NNNILabs/Pulsed-Laser-Driver/Software/Simulation/LT1193 Diff Follower GaN Simple.asc

C1: cap; 33p
C2: cap; 10p
D1: schottky; BAT54
L1: ind; 10n
R2: res; 100
R3: res; 250
SHUNT: res; 0.5
U1: LT1193
U2: GaN_LTspice_GS66502B_L3V4P1
V1: voltage; 8
V2: voltage; 8
V3: voltage; PULSE(0 2.5 100n 1p 1p 100n)
V4: voltage; 500; Rser=1
Named nets: 0, -5, +5, input, output, gate
.tran 300n
