NNNILabs/Pulsed-Laser-Driver/Software/Simulation/Simple Follower nonGaN.asc

C1: cap; 10p
L1: ind; 10n; Rser=0.1
M1: NMOS; AON6992_Bottom
R1: res; 50
SHUNT: res; 0.5
V1: voltage; PULSE(0 4.545 1u 500p 500p 1u); Rser=1
V2: voltage; 30; Rser=0.1
Named nets: 0, gate, source, drain, in
.tran 3u
