NNNILabs/Pulsed-Laser-Driver/Software/Simulation/Simple Follower.asc

C1: cap; 10p
L1: ind; 10n; Rser=0.1
R1: res; 220
R2: res; 0.01
SHUNT: res; 0.5
U1: GaN_LTspice_GS-065-008-1-L_L3V4P1
V1: voltage; PULSE(0 4.625 100n 500p 500p 100n); Rser=1
V2: voltage; 500; Rser=0.1
Named nets: 0, gate, source, drain, in
.tran 300n
