NNNILabs/Pulsed-Laser-Driver/Software/Simulation/LT1193 Diff Follower.asc

C1: cap; 220p
M1: nmos; AO6408
R1: res; 0.1
R2: res; 110
R3: res; 50
R4: res; 220
U1: LT1193
V1: voltage; 5
V2: voltage; 5
V3: voltage; PULSE(0 0.5 1u 10n 10n 1u)
V4: voltage; 20V
Named nets: 0, -5, +5, input, output
.tran 3u
